andrebandarra/para-controller-mini/photos/P1190597.JPG

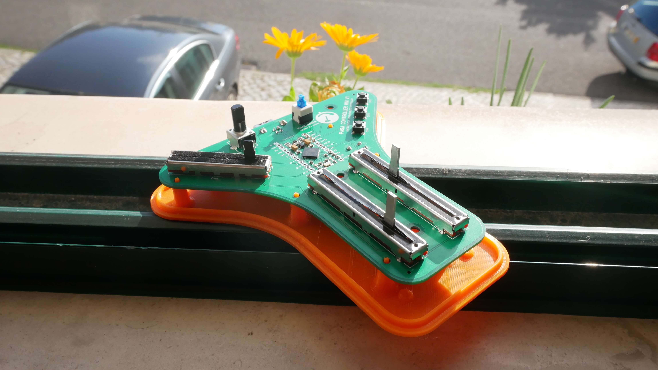
photos/P1190597.JPG
