andrebandarra/para-controller-mini/photos/P1190806.JPG

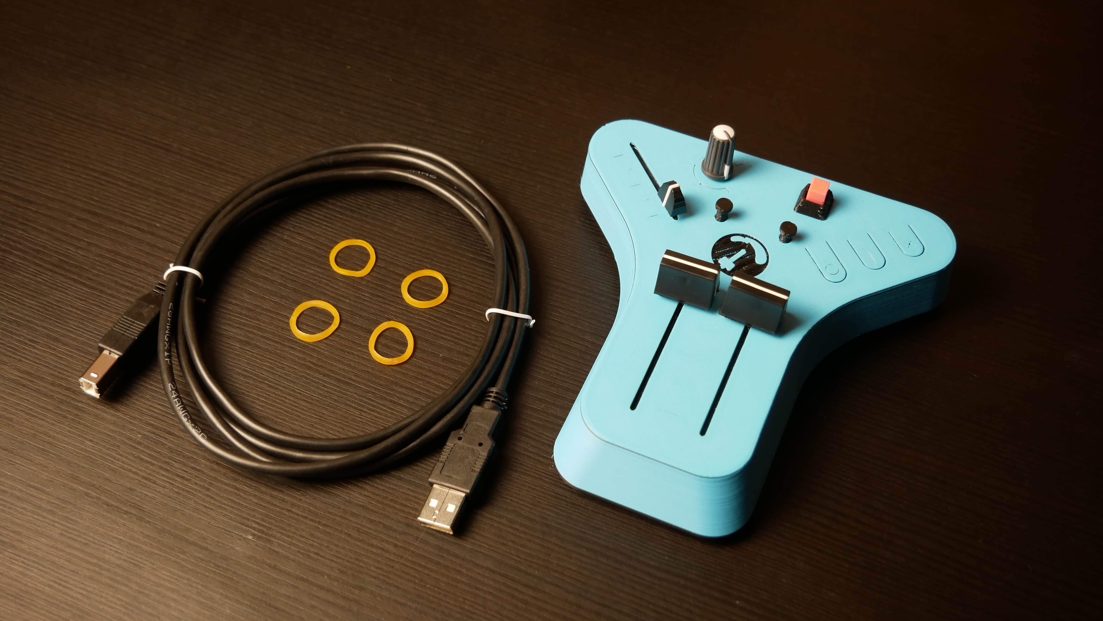
photos/P1190806.JPG
