andrebandarra/para-controller-mini/cad/parts/square cap.SLDPRT

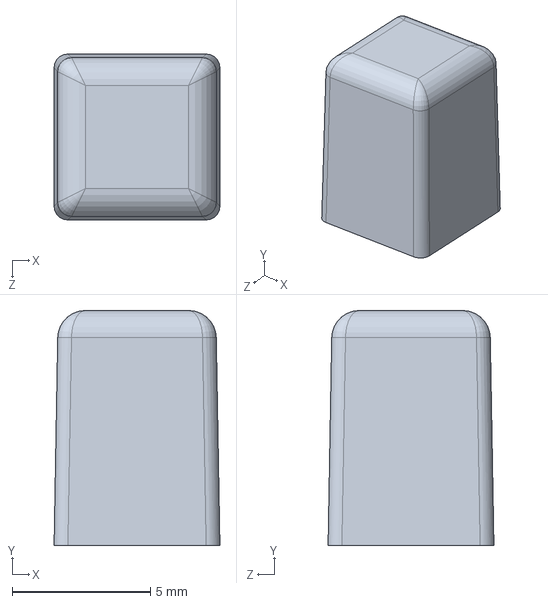
[picture p21: CAD file, 2021-11-13]
cad/parts/square cap.SLDPRT
6.00 x 8.50 x 6.00 mm
