andrebandarra/para-controller-mini/cad/parts/H8temp button.SLDPRT

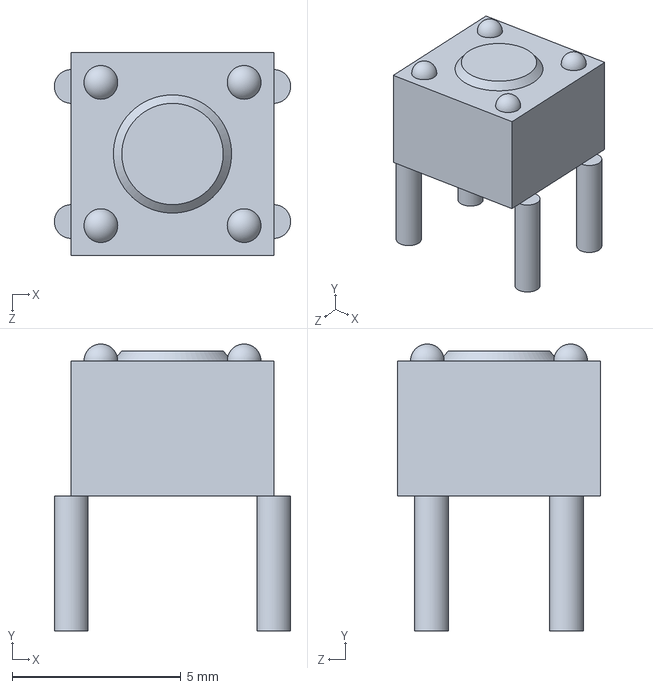
[picture p22: CAD file, 2021-11-13]
cad/parts/H8temp button.SLDPRT
7.00 x 8.50 x 6.00 mm
