andrebandarra/para-controller-mini/cad/parts/Pro_Micro.SLDPRT

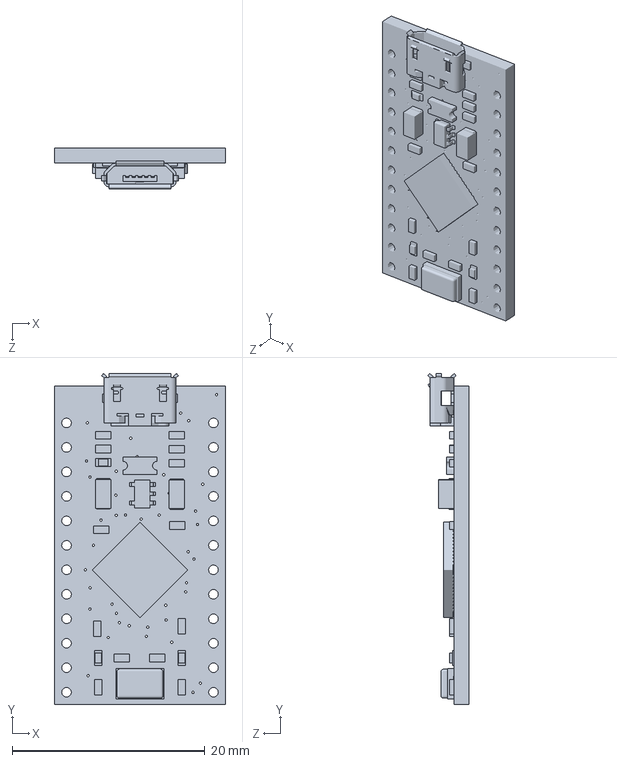
[picture p23: CAD file, 2021-11-13]
cad/parts/Pro_Micro.SLDPRT
17.8 x 34.3 x 4.30 mm
