andrebandarra/para-controller-mini/cad/parts/round button riser.SLDPRT

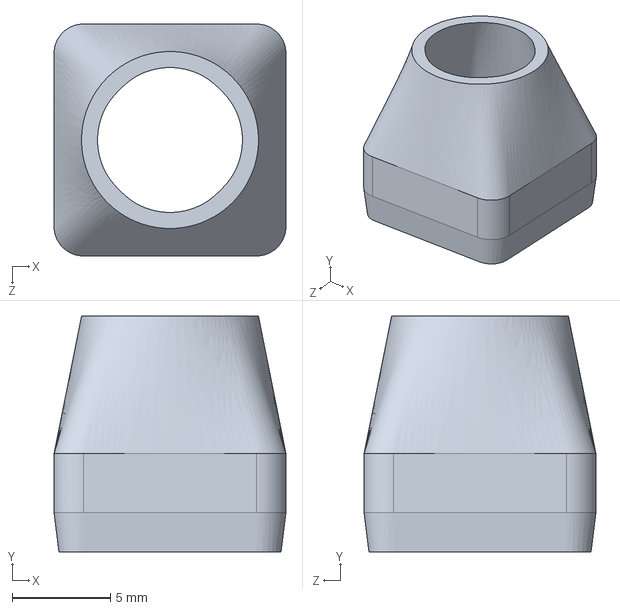
[picture p24: CAD file, 2021-11-13]
cad/parts/round button riser.SLDPRT
11.8 x 12.0 x 11.8 mm
