andrebandarra/para-controller-mini/cad/parts/rubber band peg.SLDPRT

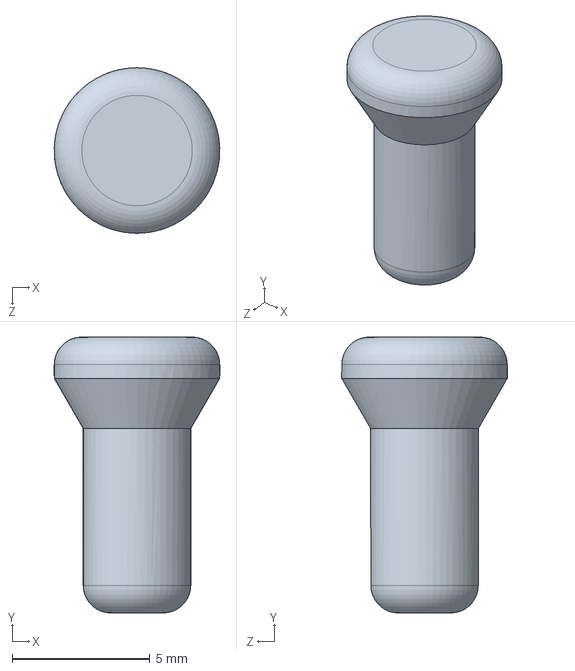
[picture p25: CAD file, 2021-11-13]
cad/parts/rubber band peg.SLDPRT
6.00 x 10.0 x 6.00 mm
