andrebandarra/para-controller-mini/cad/parts/45 slider cap.SLDPRT

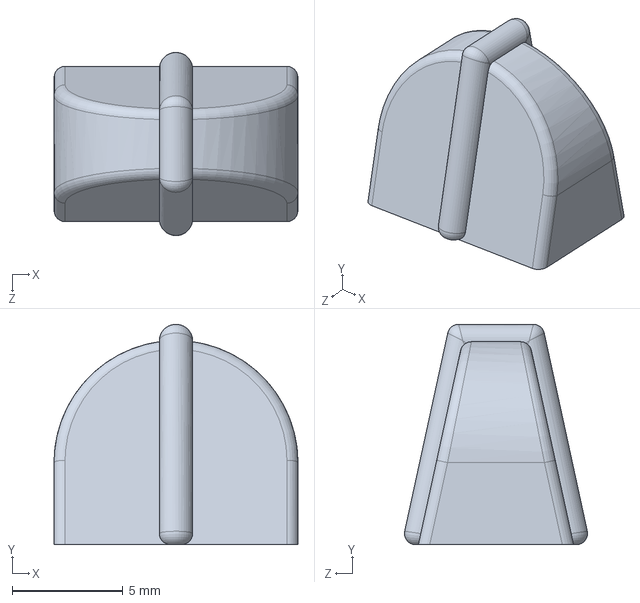
[picture p26: CAD file, 2021-11-13]
cad/parts/45 slider cap.SLDPRT
11.0 x 9.93 x 8.26 mm
