andrebandarra/para-controller-mini/cad/parts/rubber foot.SLDPRT

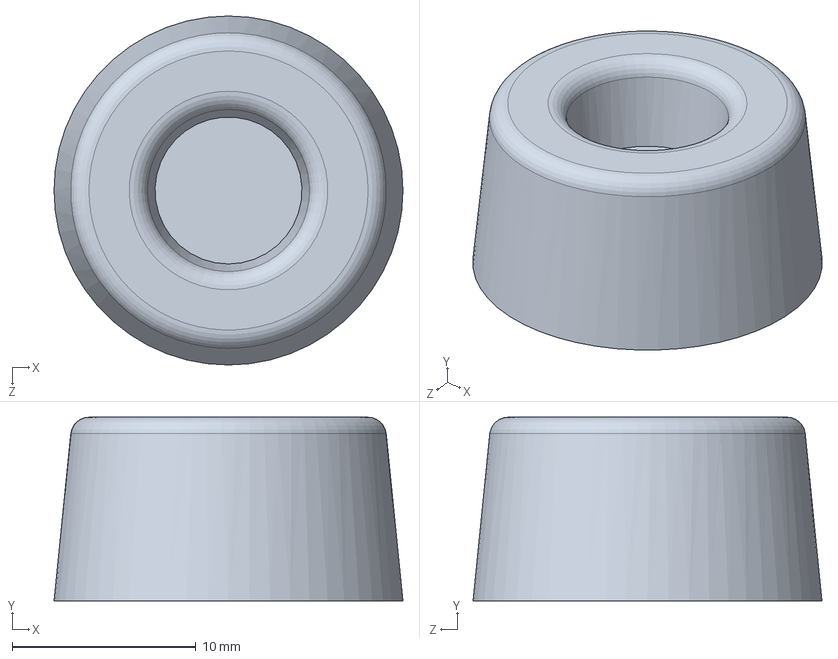
[picture p27: CAD file, 2021-11-13]
cad/parts/rubber foot.SLDPRT
19.0 x 10.0 x 19.0 mm
