andrebandarra/para-controller-mini/cad/parts/888button.SLDPRT

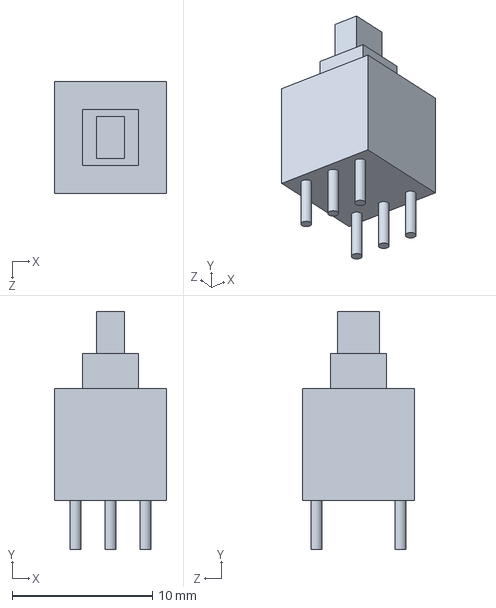
[picture p28: CAD file, 2021-11-13]
cad/parts/888button.SLDPRT
8.00 x 17.0 x 8.00 mm
