andrebandarra/para-controller-mini/cad/parts/270potA10K .SLDPRT

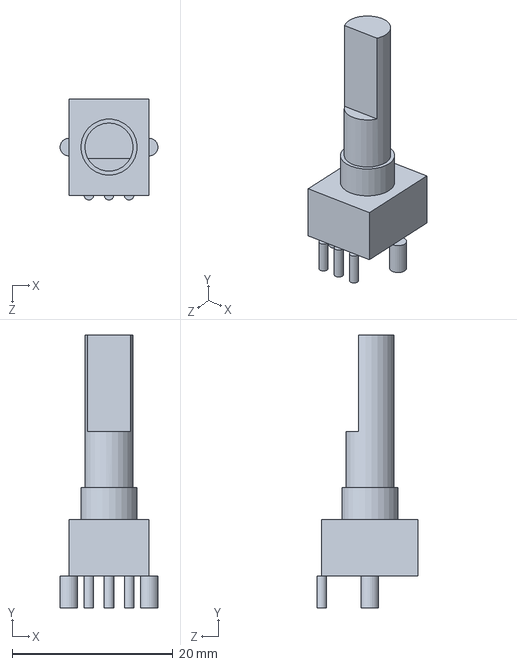
[picture p29: CAD file, 2021-11-13]
cad/parts/270potA10K .SLDPRT
12.2 x 34.0 x 12.6 mm
