andrebandarra/para-controller-mini/cad/parts/bot case.SLDPRT

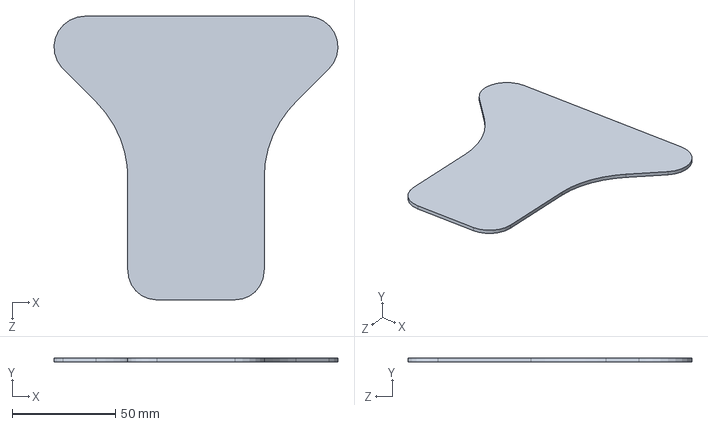
[picture p30: CAD file, 2021-11-13]
cad/parts/bot case.SLDPRT
137.8 x 2.00 x 137.6 mm
