andrebandarra/para-controller-mini/cad/parts/45 slider peg.SLDPRT

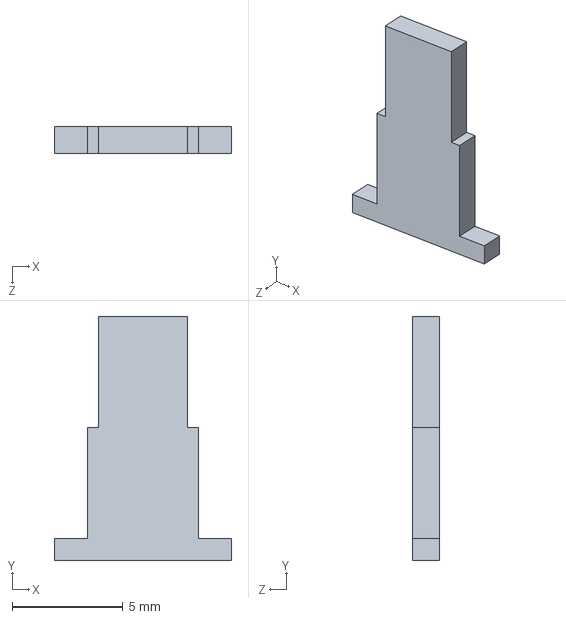
[picture p31: CAD file, 2021-11-13]
cad/parts/45 slider peg.SLDPRT
8.00 x 11.0 x 1.20 mm
