andrebandarra/para-controller-mini/cad/parts/foot rubber.SLDPRT

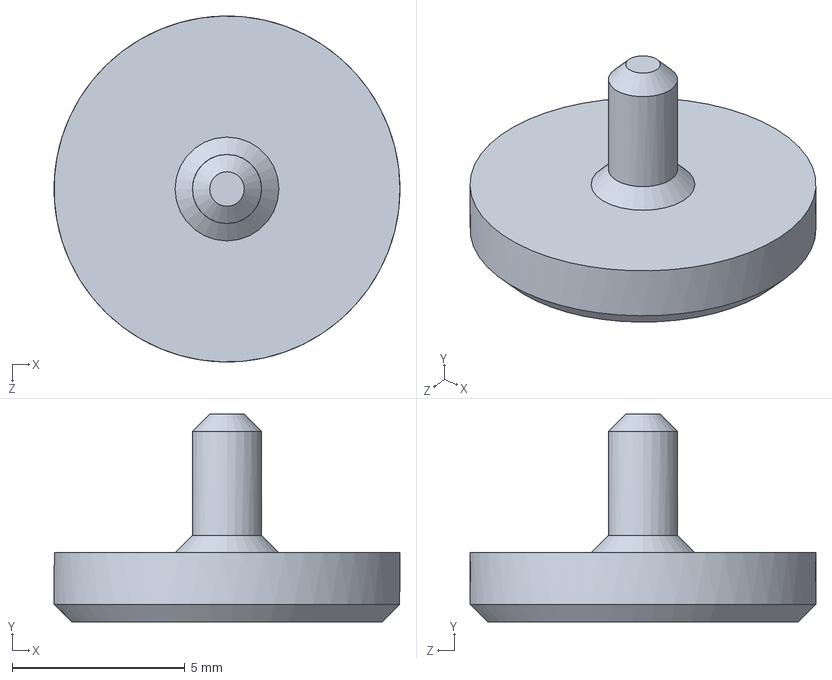
[picture p32: CAD file, 2021-11-13]
cad/parts/foot rubber.SLDPRT
10.0 x 6.00 x 10.00 mm
