andrebandarra/para-controller-mini/cad/parts/60 slider cap.SLDPRT

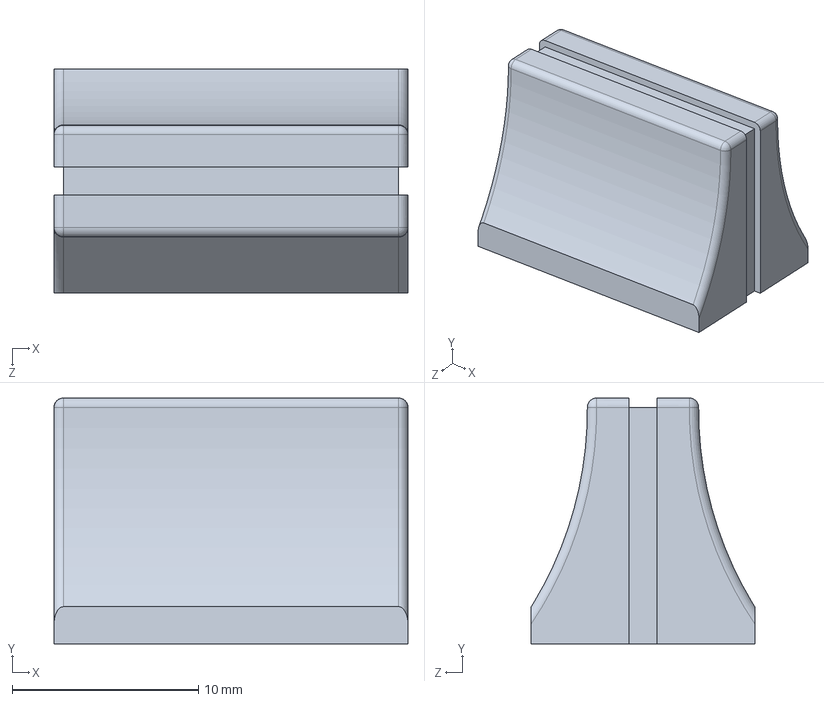
[picture p33: CAD file, 2021-11-13]
cad/parts/60 slider cap.SLDPRT
19.0 x 13.2 x 12.0 mm
