andrebandarra/para-controller-mini/cad/parts/square button riser.SLDPRT

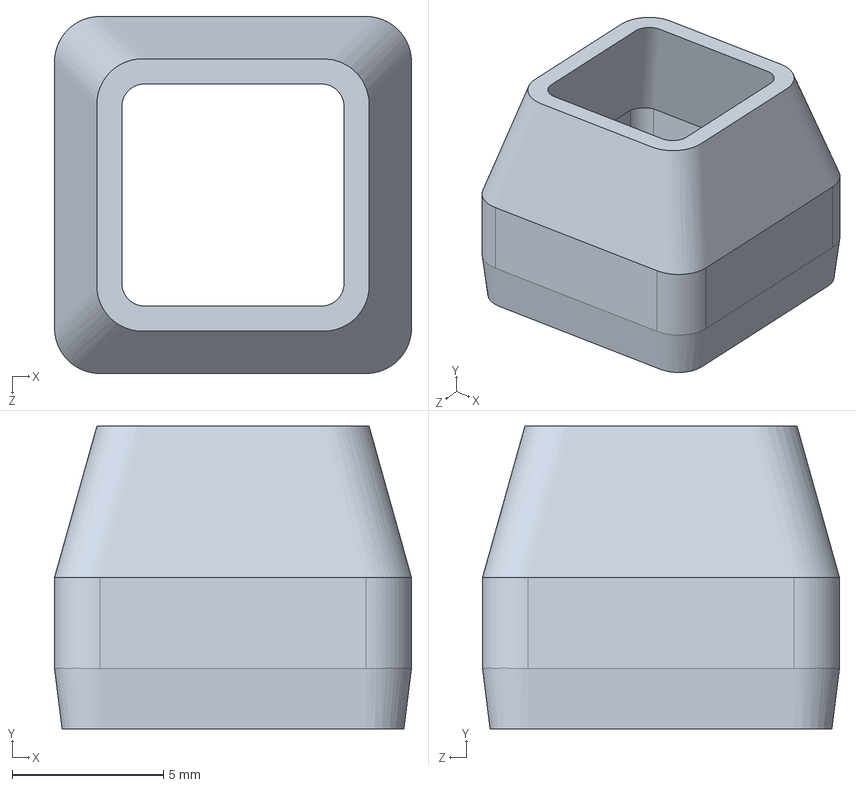
[picture p34: CAD file, 2021-11-13]
cad/parts/square button riser.SLDPRT
11.8 x 10.0 x 11.8 mm
