andrebandarra/para-controller-mini/cad/parts/button plug.SLDPRT

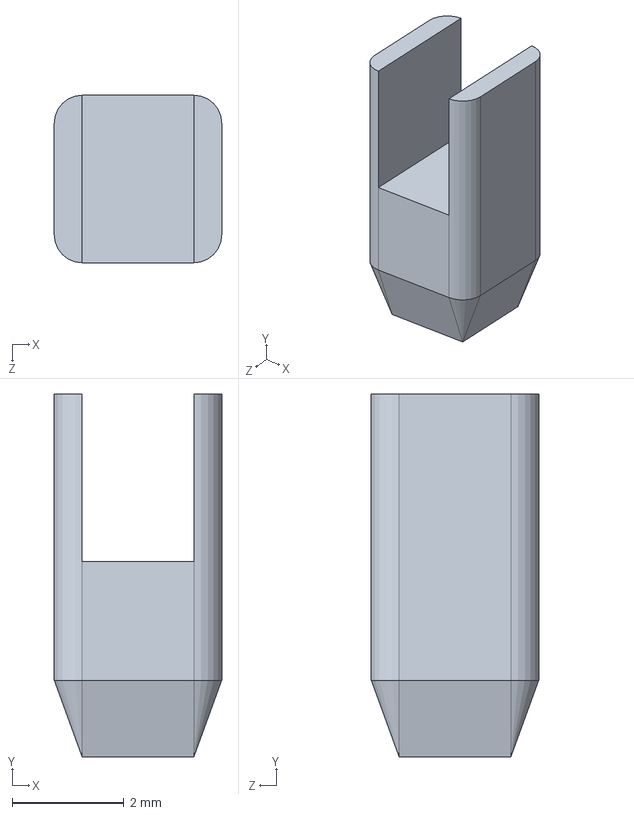
[picture p35: CAD file, 2021-11-13]
cad/parts/button plug.SLDPRT
3.00 x 6.50 x 3.00 mm
