andrebandarra/para-controller-mini/cad/parts/90deghalfaxispotcat6mm.SLDPRT

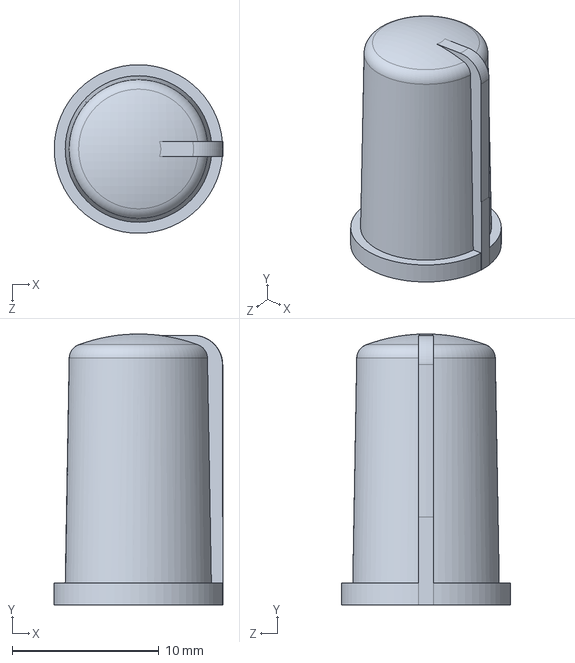
[picture p36: CAD file, 2021-11-13]
cad/parts/90deghalfaxispotcat6mm.SLDPRT
11.5 x 18.5 x 11.5 mm
