andrebandarra/para-controller-mini/cad/parts/270potB10K half shaft.SLDPRT

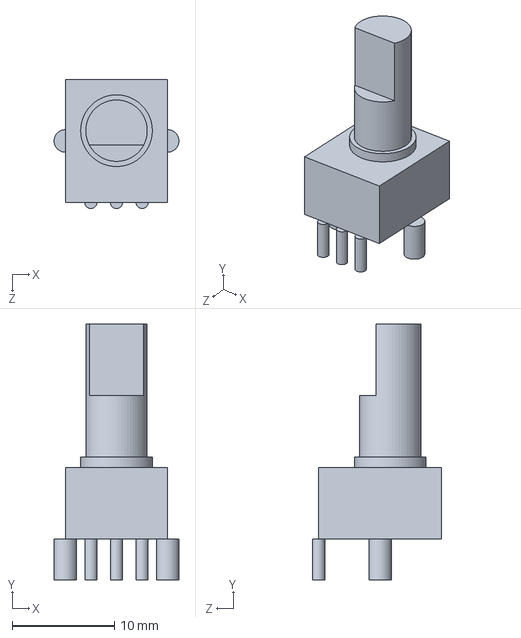
[picture p37: CAD file, 2021-11-13]
cad/parts/270potB10K half shaft.SLDPRT
12.2 x 25.0 x 12.6 mm
