andrebandarra/para-controller-mini/cad/parts/bot case1.SLDPRT

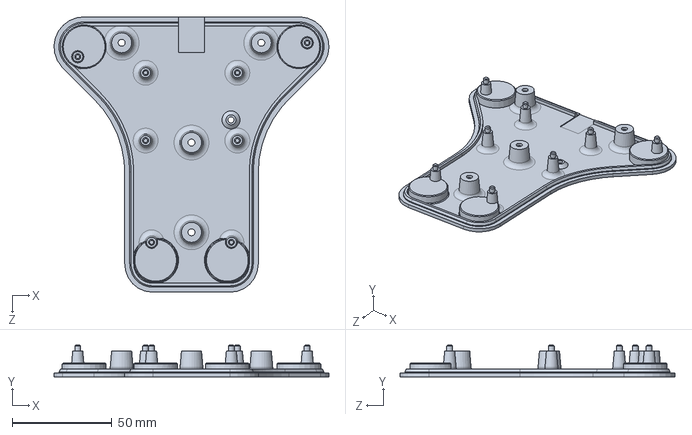
[picture p38: CAD file, 2021-11-13]
cad/parts/bot case1.SLDPRT
137.8 x 16.0 x 138.0 mm
