andrebandarra/para-controller-mini/cad/parts/45 slider body.SLDPRT

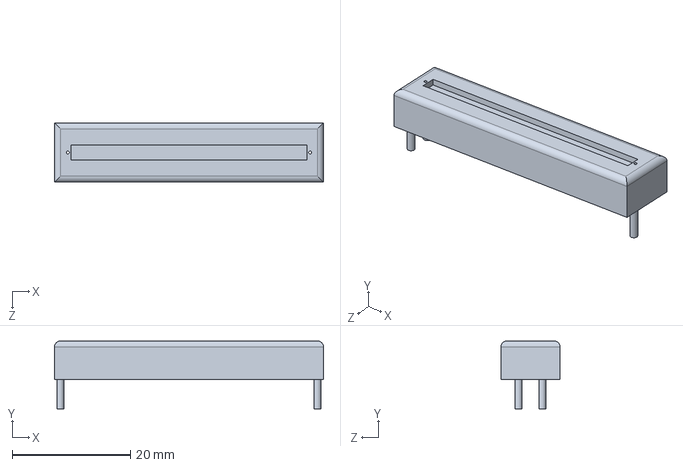
[picture p39: CAD file, 2021-11-13]
cad/parts/45 slider body.SLDPRT
45.5 x 11.5 x 10.0 mm
